josefadamcik/SofleKeyboard/docs/images/render_pcb.png

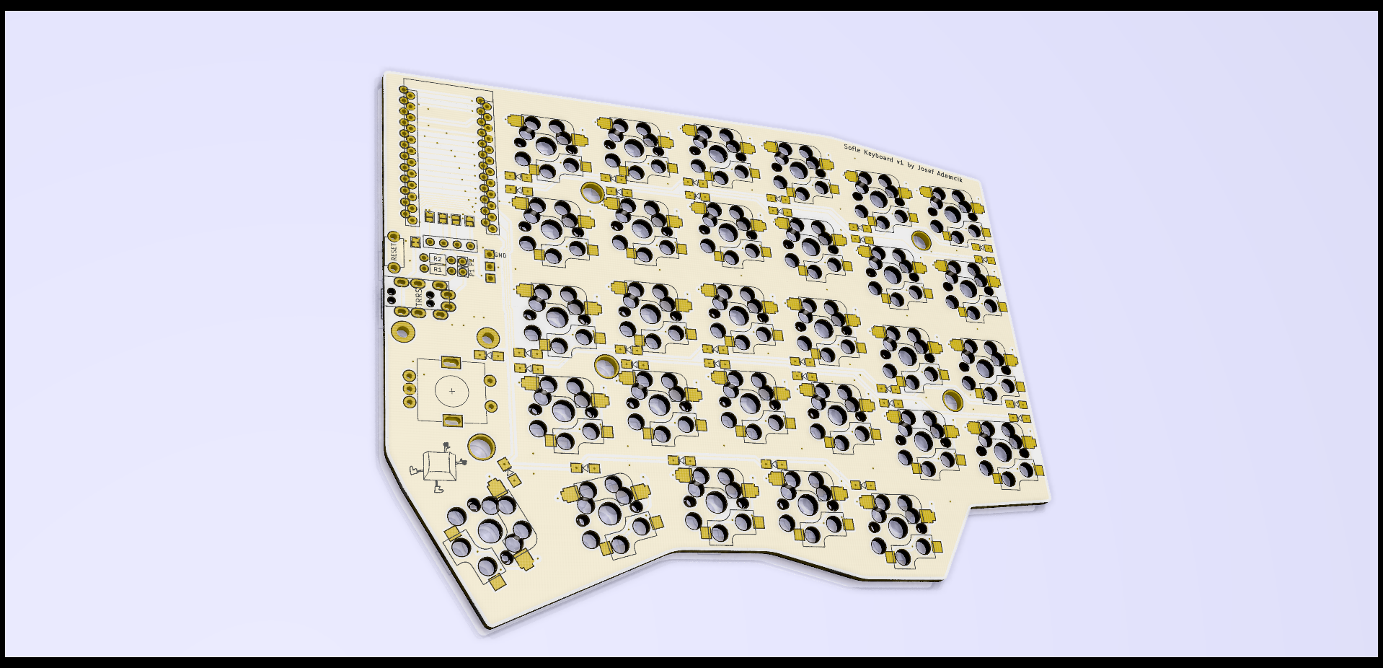
docs/images/render_pcb.png
