josefadamcik/SofleKeyboard/docs/images/soflekeyboard_layout_adjust.png

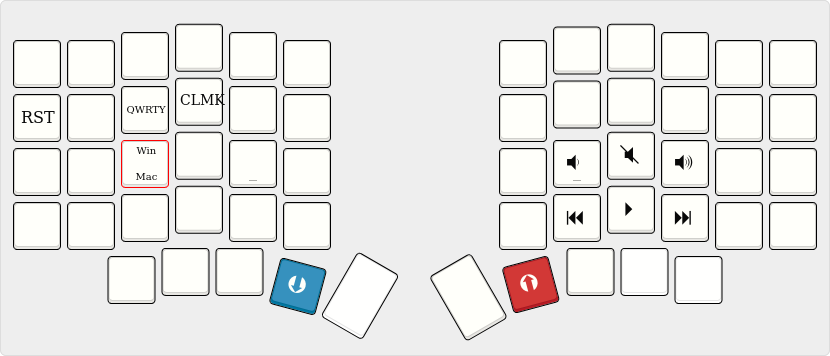
docs/images/soflekeyboard_layout_adjust.png
