josefadamcik/SofleKeyboard/docs/images/SofleKeyboardBottomPlate.png

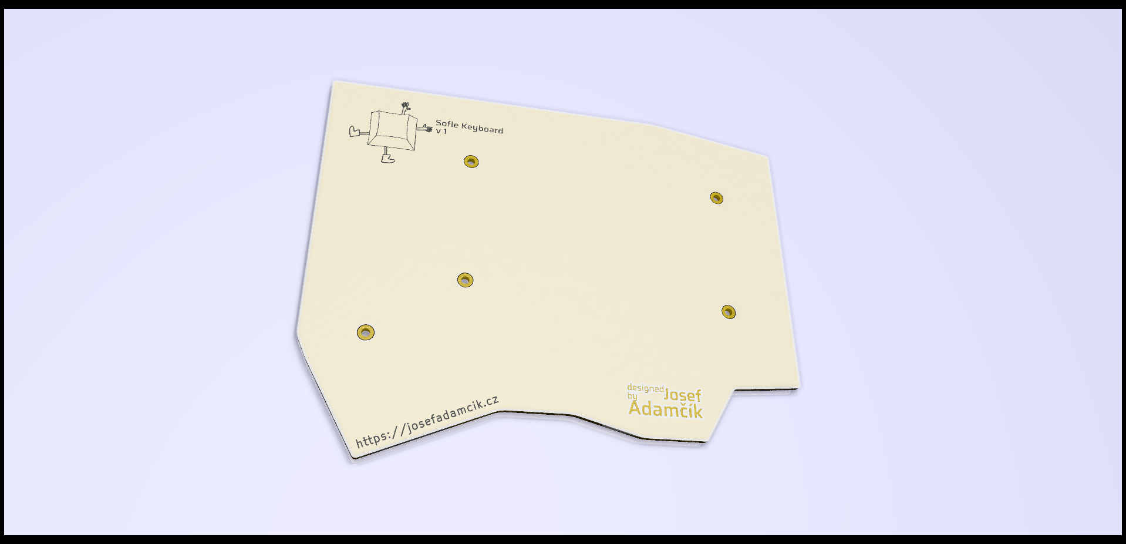
docs/images/SofleKeyboardBottomPlate.png
