josefadamcik/SofleKeyboard/docs/images/SofleKeyboardTopPlate.png

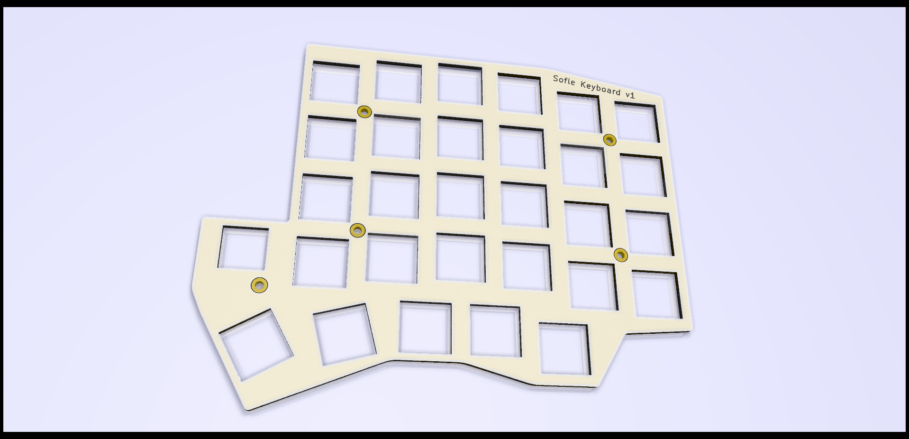
docs/images/SofleKeyboardTopPlate.png
