josefadamcik/SofleKeyboard/Images/SofleKeyboard2-freecad.png

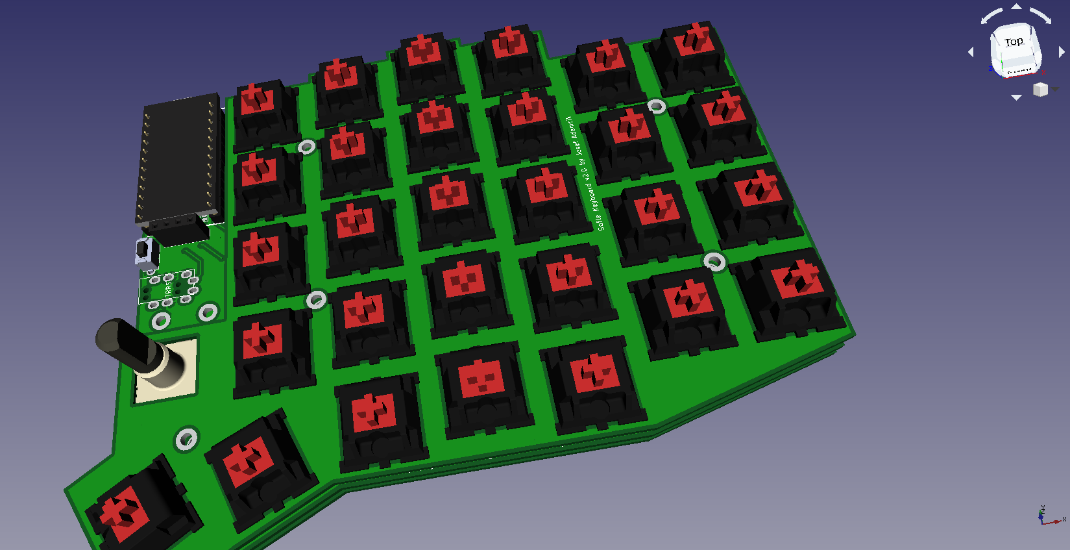
Images/SofleKeyboard2-freecad.png
