josefadamcik/SofleKeyboard/Images/SofleKeyboard2_bottom_plate_render.jpg

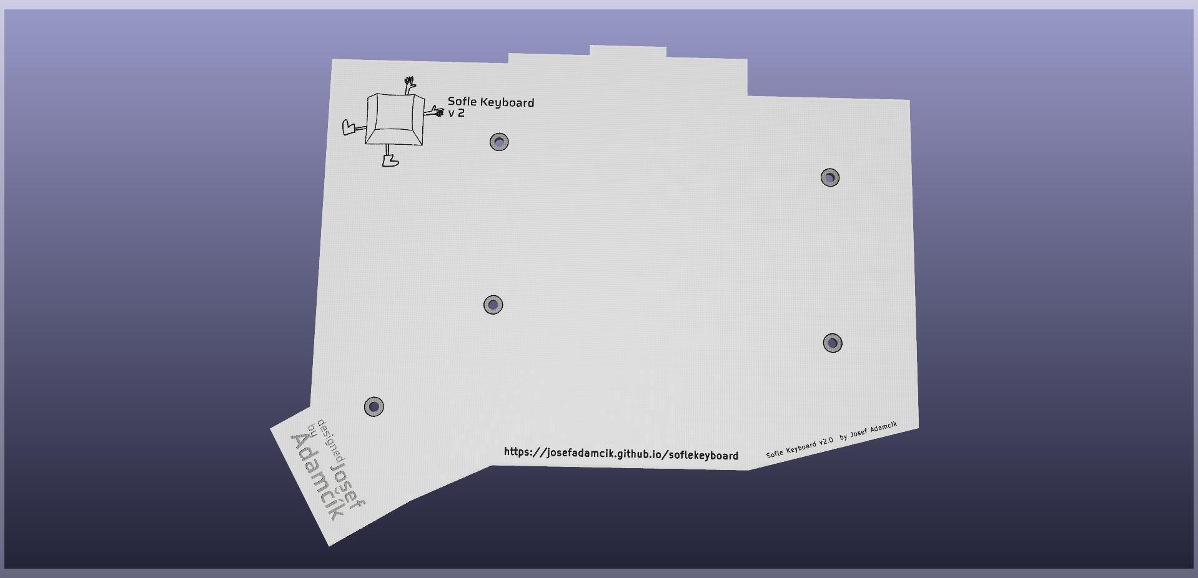
Images/SofleKeyboard2_bottom_plate_render.jpg
