josefadamcik/SofleKeyboard/Images/SofleKeyboard2_render1.jpg

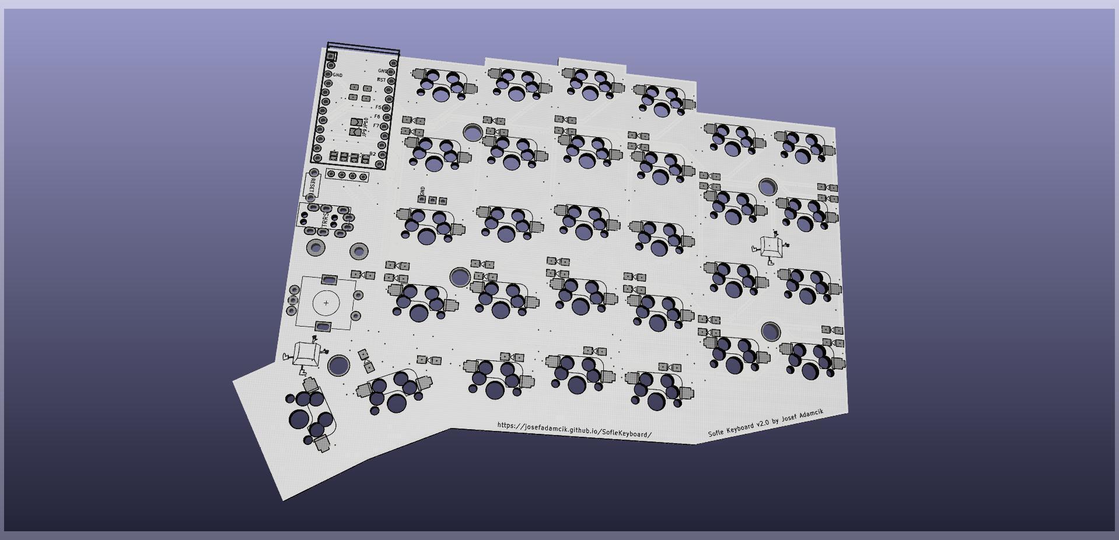
Images/SofleKeyboard2_render1.jpg
