josefadamcik/SofleKeyboard/Images/SofleKeyboard2_render2.jpg

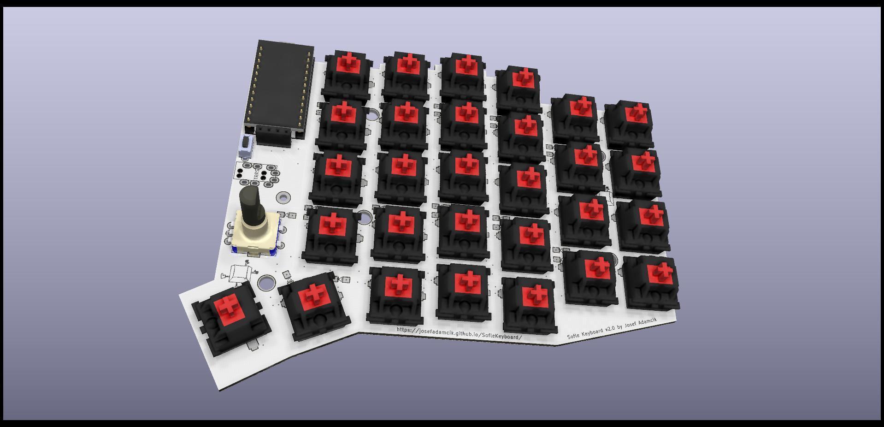
Images/SofleKeyboard2_render2.jpg
