josefadamcik/SofleKeyboard/Images/SofleKeyboard2_render3.jpg

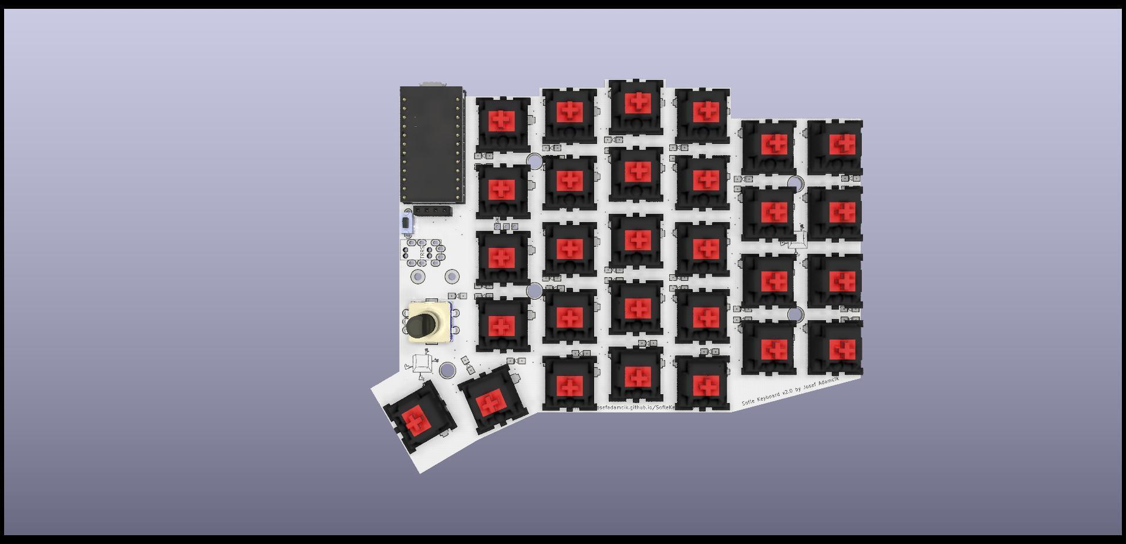
Images/SofleKeyboard2_render3.jpg
