josefadamcik/SofleKeyboard/Images/SofleKeyboard2_render4.jpg

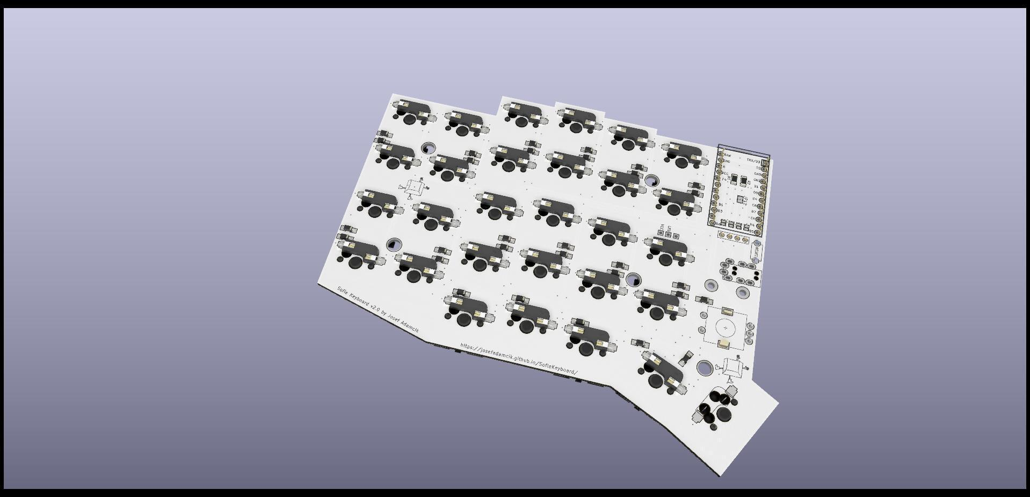
Images/SofleKeyboard2_render4.jpg
