josefadamcik/SofleKeyboard/Images/SofleKeyboard2_top_plate_render.jpg

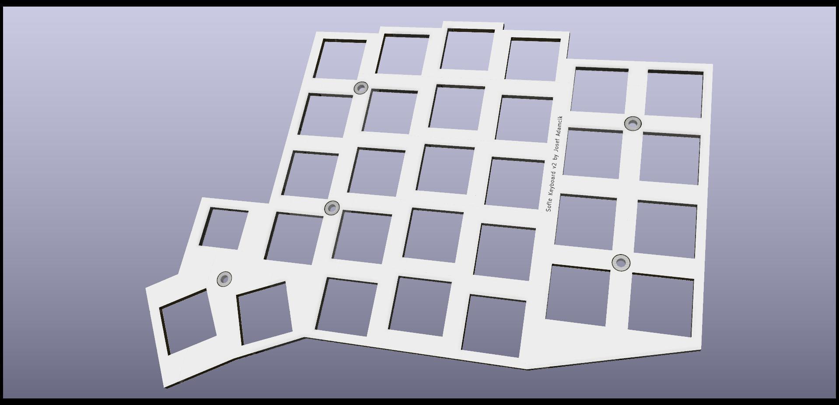
Images/SofleKeyboard2_top_plate_render.jpg
