josefadamcik/SofleKeyboard/docs/images/build_guide/IMG_20191106_204329.jpg

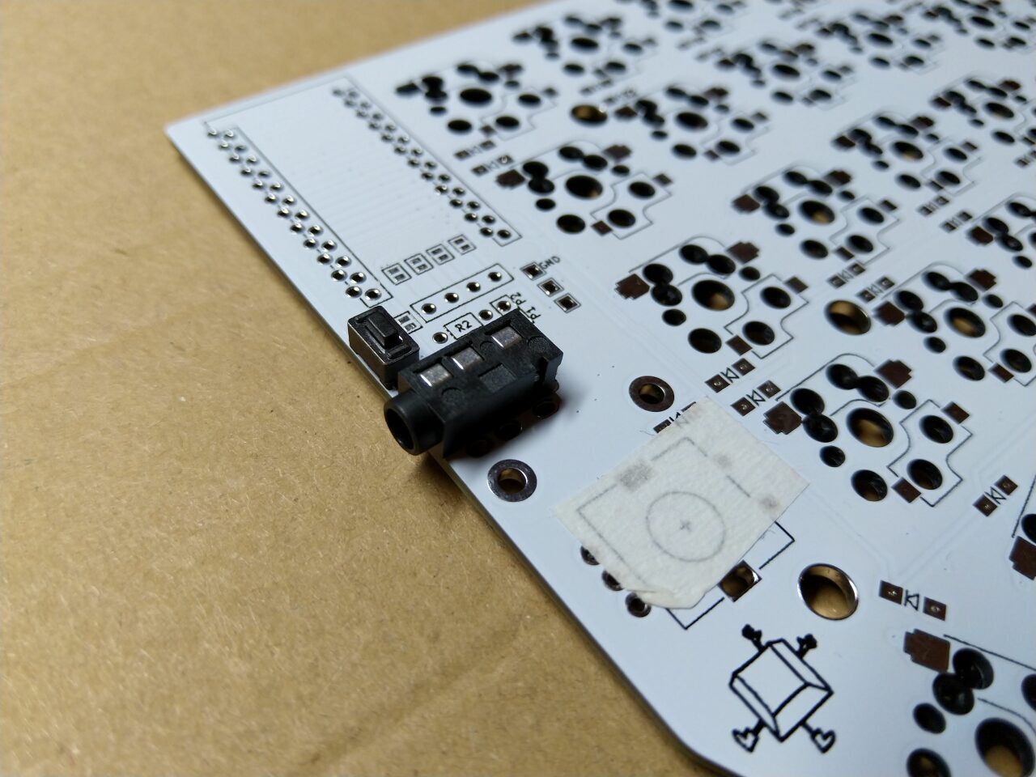
docs/images/build_guide/IMG_20191106_204329.jpg
