josefadamcik/SofleKeyboard/docs/images/build_guide/IMG_20191106_205956.jpg

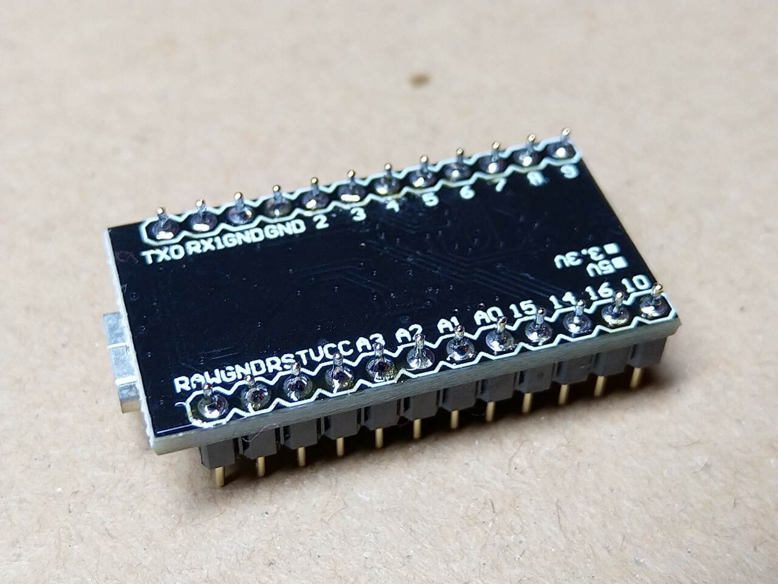
docs/images/build_guide/IMG_20191106_205956.jpg
