josefadamcik/SofleKeyboard/docs/images/build_guide/IMG_20191106_211037.jpg

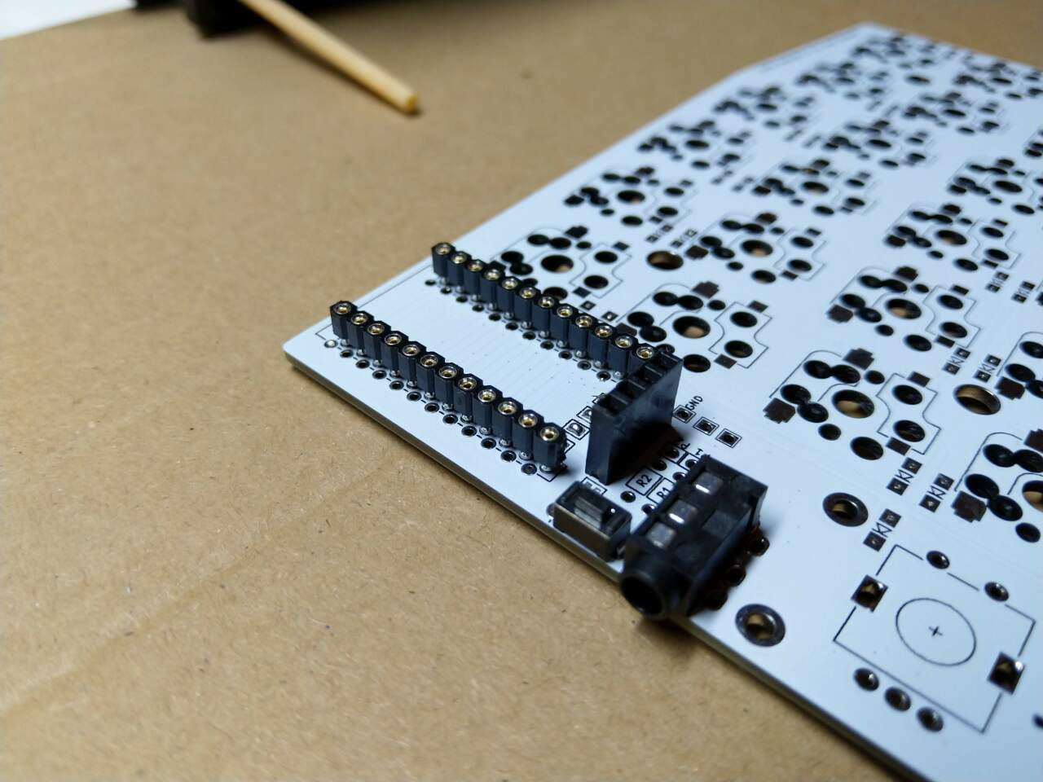
docs/images/build_guide/IMG_20191106_211037.jpg
