josefadamcik/SofleKeyboard/docs/images/build_guide/micro_placement_v2.jpg

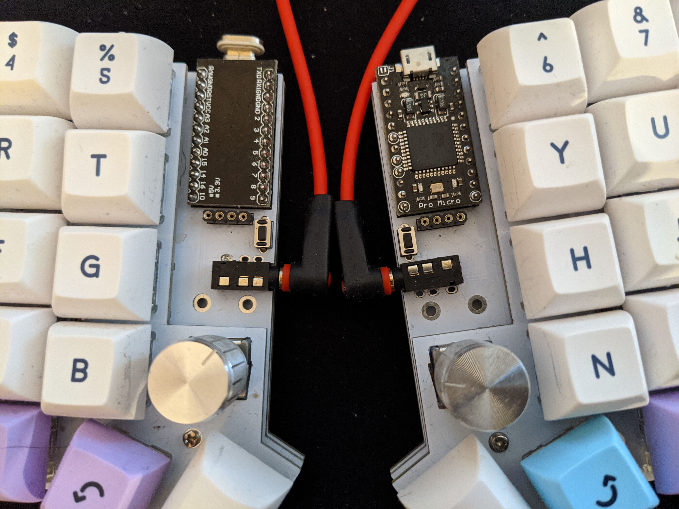
docs/images/build_guide/micro_placement_v2.jpg
